rtitmuss/tornblue/img/PXL_20220306_111358722.jpg

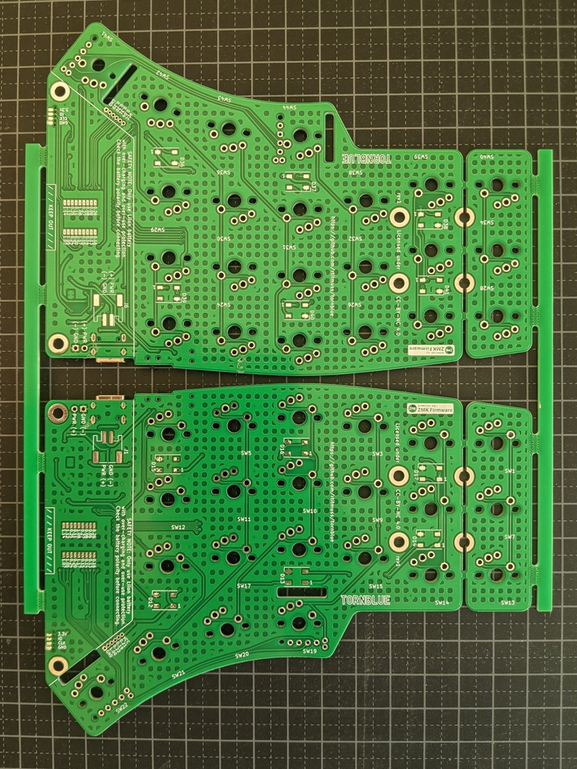
img/PXL_20220306_111358722.jpg
