rtitmuss/tornblue/pcb/tornblue.kicad_sch

## KiCad design pcb/tornblue.kicad_sch (2022-01-09)

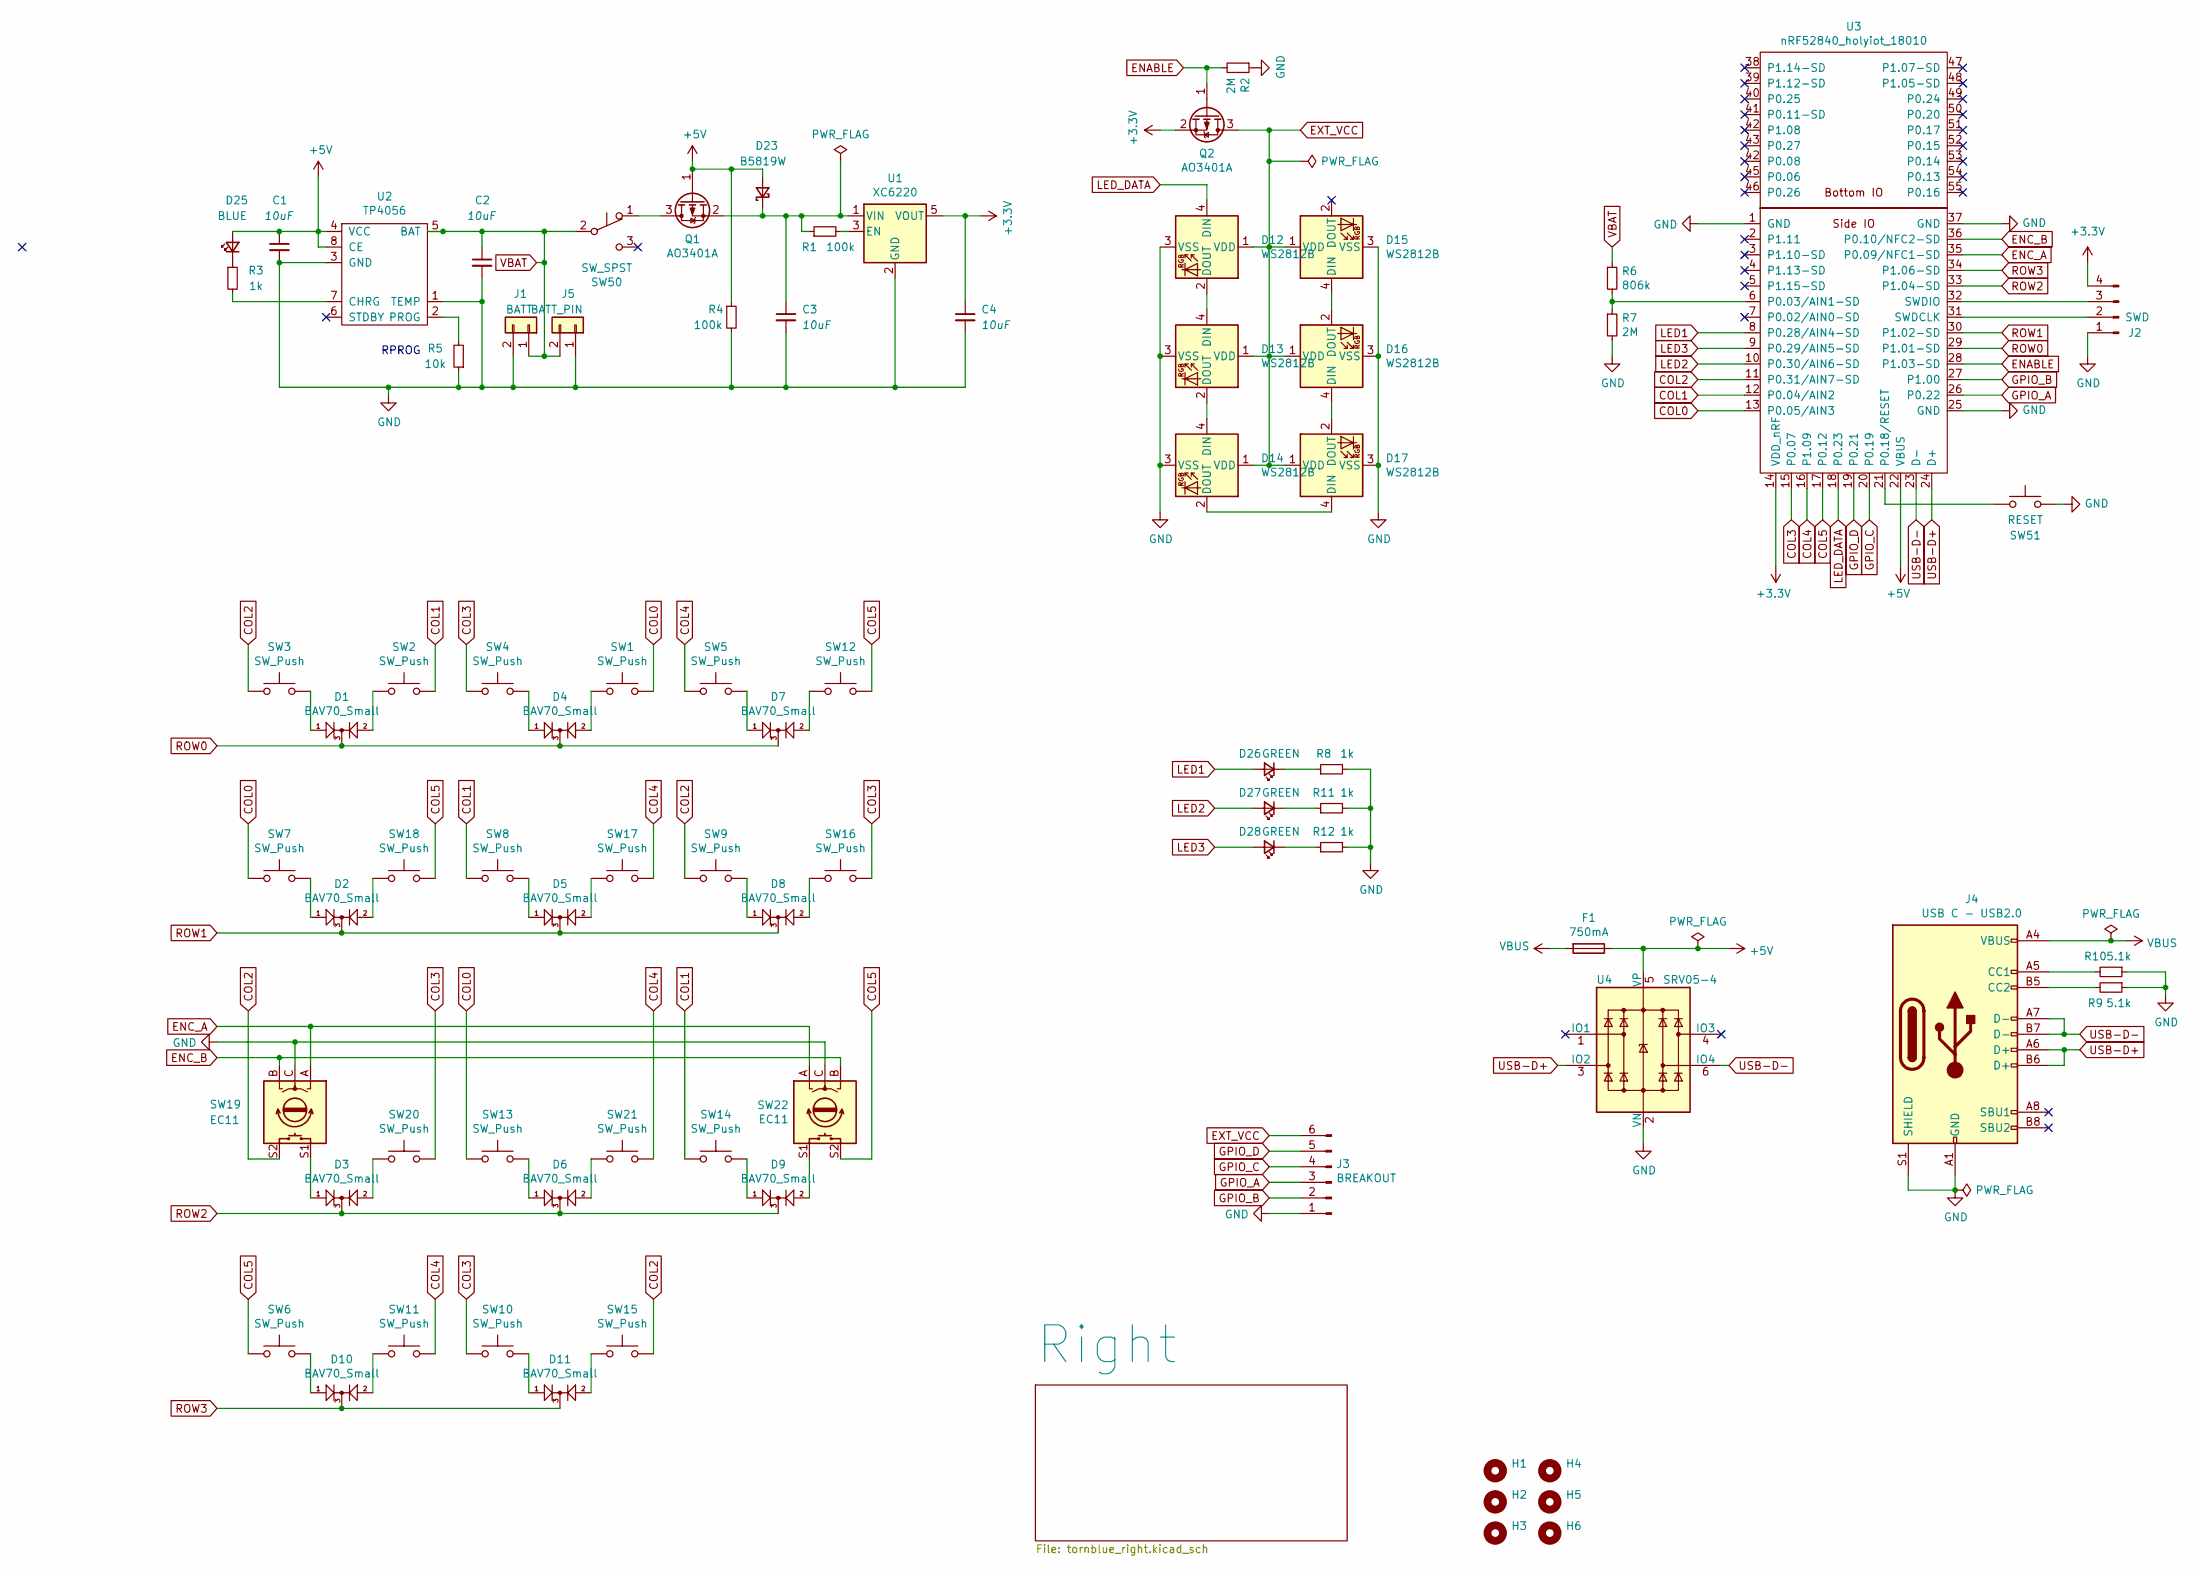
[picture p37: schematic tornblue.kicad_sch]

Parts:
C1, C2, C3, C4: 10uF; D_0805_2012Metric; PartNumber CL21A106KAYNNNE; LCSC C15850
D1, D2, D3, D4, D5, D6, D7, D8, D9, D10, D11: BAV70_Small; SOT-23; PartNumber BAV70; LCSC C68978
D12, D13, D14, D15, D16, D17: WS2812B; LED_WS2812B_PLCC4_5.0x5.0mm_P3.2mm; LCSC C2761795
D23: B5819W; D_SOD-123; PartNumber B5819W SL; LCSC C8598
D25: BLUE; LED_0805_2012Metric; PartNumber 17-21/BHC-AP1Q2/3T; LCSC C99870
D26, D27, D28: GREEN; LED_0805_2012Metric; PartNumber MHT170UGCT; LCSC C397047
F1: 750mA; Fuse_1206_3216Metric; PartNumber CC12H750MA-TR; LCSC C328915
H1, H2, H3, H4: MountingHole; MountingHole_3.2mm_M3_DIN965_Pad
H5, H6: MountingHole; MountingHole_3.2mm_M3_DIN965_Pad_Slot
J1: BATT; JST_PH_S2B-PH-SM4-TB_1x02-1MP_P2.00mm_Horizontal; LCSC C295747
J2: SWD; SOIC_clipProgSmall
J3: BREAKOUT; PinHeader_1x06_P1.27mm_Vertical
J4: USB C - USB2.0; USB_C_Receptacle_XKB_U262-16XN-4BVC11; PartNumber 918-418K2023S40001; LCSC C167321
J5: BATT_PIN; PinHeader_1x02_P2.54mm_Vertical
Q1, Q2: AO3401A; SOT-23; PartNumber AO3401A; LCSC C15127
R1, R4: 100k; R_0805_2012Metric; PartNumber 0805W8F1003T5E; LCSC C17407
R2, R7: 2M; R_0805_2012Metric; PartNumber 0805W8F2004T5E; LCSC C26112
R3, R8, R11, R12: 1k; R_0805_2012Metric; PartNumber 0805W8F1001T5E; LCSC C17513
R5: 10k; R_0805_2012Metric; PartNumber 0805W8F1002T5E; LCSC C17414
R6: 806k; R_0805_2012Metric; PartNumber 0805W8F8063T5E; LCSC C63494
R9, R10: 5.1k; R_0805_2012Metric; PartNumber 0805W8F5101T5E; LCSC C27834
SW1, SW2, SW3, SW4, SW5, SW6, SW7, SW8, SW9, SW10, SW11, SW12, SW13, SW14, SW15, SW16, SW17, SW18, SW20, SW21: SW_Push; MX_PG1350_optional
SW19, SW22: EC11; MX_PG1350_EVQWGD001_LR_optional
SW50: SW_SPST; SW_SPDT_PCM12; PartNumber PCM12SMTR; LCSC C221841
SW51: RESET; SW_SPST_EVQPUC02K; PartNumber EVQPUC02K; LCSC C79174
U1: XC6220; SOT-23-5; PartNumber XC6220B331MR-G; LCSC C86534
U2: TP4056; SOIC-8-1EP_3.9x4.9mm_P1.27mm_EP2.29x3mm_ThermalVias; PartNumber TP4056-42-ESOP8; LCSC C16581
U3: nRF52840_holyiot_18010; PartNumber YJ-18010-nRF52840; LCSC nRF52840_holyiot_18010
U4: SRV05-4; SOT-23-6; PartNumber SRV05-4-P-T7; LCSC C85364

Connections:
+3.3V: C4.1, J2.4, Q2.2 (S), U1.5 (VOUT), U3.14 (VDD_nRF)
+5V: C1.1, D23.2 (A), D25.2 (A), F1.1, Q1.1 (G), R4.1, U2.4 (VCC), U2.8 (CE), U3.22 (VBUS), U4.5 (VP)
COL0: SW1.1, SW7.1, SW13.1, U3.13 (P0.05/AIN3)
COL1: SW2.1, SW8.1, SW14.1, U3.12 (P0.04/AIN2)
COL2: SW3.1, SW9.1, SW15.1, SW19.S2, U3.11 (P0.31/AIN7-SD)
COL3: SW4.1, SW10.1, SW16.1, SW20.1, U3.15 (P0.07)
COL4: SW5.1, SW11.1, SW17.1, SW21.1, U3.16 (P1.09)
COL5: SW6.1, SW12.1, SW18.1, SW22.S2, U3.17 (P0.12)
ENABLE: Q2.1 (G), R2.2, U3.28 (P1.03-SD)
ENC_A: SW19.A, SW22.A, U3.35 (P0.09/NFC1-SD)
ENC_B: SW19.B, SW22.B, U3.36 (P0.10/NFC2-SD)
EXT_VCC: D12.1 (VDD), D13.1 (VDD), D14.1 (VDD), D15.1 (VDD), D16.1 (VDD), D17.1 (VDD), J3.6, Q2.3 (D)
GND: C1.2, C2.2, C3.2, C4.2, D12.3 (VSS), D13.3 (VSS), D14.3 (VSS), D15.3 (VSS), D16.3 (VSS), D17.3 (VSS), J1.2, J2.1, J3.1, J4.A1 (GND), J4.A12 (GND), J4.B1 (GND), J4.B12 (GND), J4.S1 (SHIELD), J5.1, R2.1, R4.2, R5.1, R7.2, R8.2, R9.1, R10.1, R11.2, R12.2, SW19.C, SW22.C, SW51.2, U1.2 (GND), U2.1 (TEMP), U2.3 (GND), U3.1 (GND), U3.25 (GND), U3.37 (GND), U4.2 (VN)
GPIO_A: J3.3, U3.26 (P0.22)
GPIO_B: J3.2, U3.27 (P1.00)
GPIO_C: J3.4, U3.20 (P0.19)
GPIO_D: J3.5, U3.19 (P0.21)
LED1: D26.2 (A), U3.8 (P0.28/AIN4-SD)
LED2: D27.2 (A), U3.10 (P0.30/AIN6-SD)
LED3: D28.2 (A), U3.9 (P0.29/AIN5-SD)
LED_DATA: D12.4 (DIN), U3.18 (P0.23)
unnamed: C3.1, D23.1 (K), Q1.2 (S), R1.1, U1.1 (VIN)
unnamed: D1.1 (A1), SW3.2
unnamed: D1.2 (A2), SW2.2
unnamed: D2.1 (A1), SW7.2
unnamed: D2.2 (A2), SW18.2
unnamed: D3.1 (A1), SW19.S1
unnamed: D3.2 (A2), SW20.2
unnamed: D4.1 (A1), SW4.2
unnamed: D4.2 (A2), SW1.2
unnamed: D5.1 (A1), SW8.2
unnamed: D5.2 (A2), SW17.2
unnamed: D6.1 (A1), SW13.2
unnamed: D6.2 (A2), SW21.2
unnamed: D7.1 (A1), SW5.2
unnamed: D7.2 (A2), SW12.2
unnamed: D8.1 (A1), SW9.2
unnamed: D8.2 (A2), SW16.2
unnamed: D9.1 (A1), SW14.2
unnamed: D9.2 (A2), SW22.S1
unnamed: D10.1 (A1), SW6.2
unnamed: D10.2 (A2), SW11.2
unnamed: D11.1 (A1), SW10.2
unnamed: D11.2 (A2), SW15.2
unnamed: D12.2 (DOUT), D13.4 (DIN)
unnamed: D13.2 (DOUT), D14.4 (DIN)
unnamed: D14.2 (DOUT), D17.4 (DIN)
unnamed: D15.4 (DIN), D16.2 (DOUT)
unnamed: D16.4 (DIN), D17.2 (DOUT)
unnamed: D25.1 (K), R3.1
unnamed: D26.1 (K), R8.1
unnamed: D27.1 (K), R11.1
unnamed: D28.1 (K), R12.1
unnamed: J2.2, U3.31 (SWDCLK)
unnamed: J2.3, U3.32 (SWDIO)
unnamed: J4.A5 (CC1), R10.2
unnamed: J4.B5 (CC2), R9.2
unnamed: Q1.3 (D), SW50.1 (A)
unnamed: R1.2, U1.3 (EN)
unnamed: R3.2, U2.7 (CHRG)
unnamed: R5.2, U2.2 (PROG)
unnamed: R6.2, R7.1, U3.6 (P0.03/AIN1-SD)
unnamed: SW51.1, U3.21 (P0.18/RESET)
ROW0: D1.3 (K), D4.3 (K), D7.3 (K), U3.29 (P1.01-SD)
ROW1: D2.3 (K), D5.3 (K), D8.3 (K), U3.30 (P1.02-SD)
ROW2: D3.3 (K), D6.3 (K), D9.3 (K), U3.33 (P1.04-SD)
ROW3: D10.3 (K), D11.3 (K), U3.34 (P1.06-SD)
USB-D+: J4.A6 (D+), J4.B6 (D+), U3.24 (D+), U4.3 (IO2)
USB-D-: J4.A7 (D-), J4.B7 (D-), U3.23 (D-), U4.6 (IO4)
VBAT: C2.1, J1.1, J5.2, R6.1, SW50.2 (B), U2.5 (BAT)
VBUS: F1.2, J4.A4 (VBUS), J4.A9 (VBUS), J4.B4 (VBUS), J4.B9 (VBUS)

Notes on the sheet:
RPROG
