rtitmuss/tornblue/pcb/tornblue_right.kicad_sch

## KiCad design pcb/tornblue_right.kicad_sch (2022-01-09)

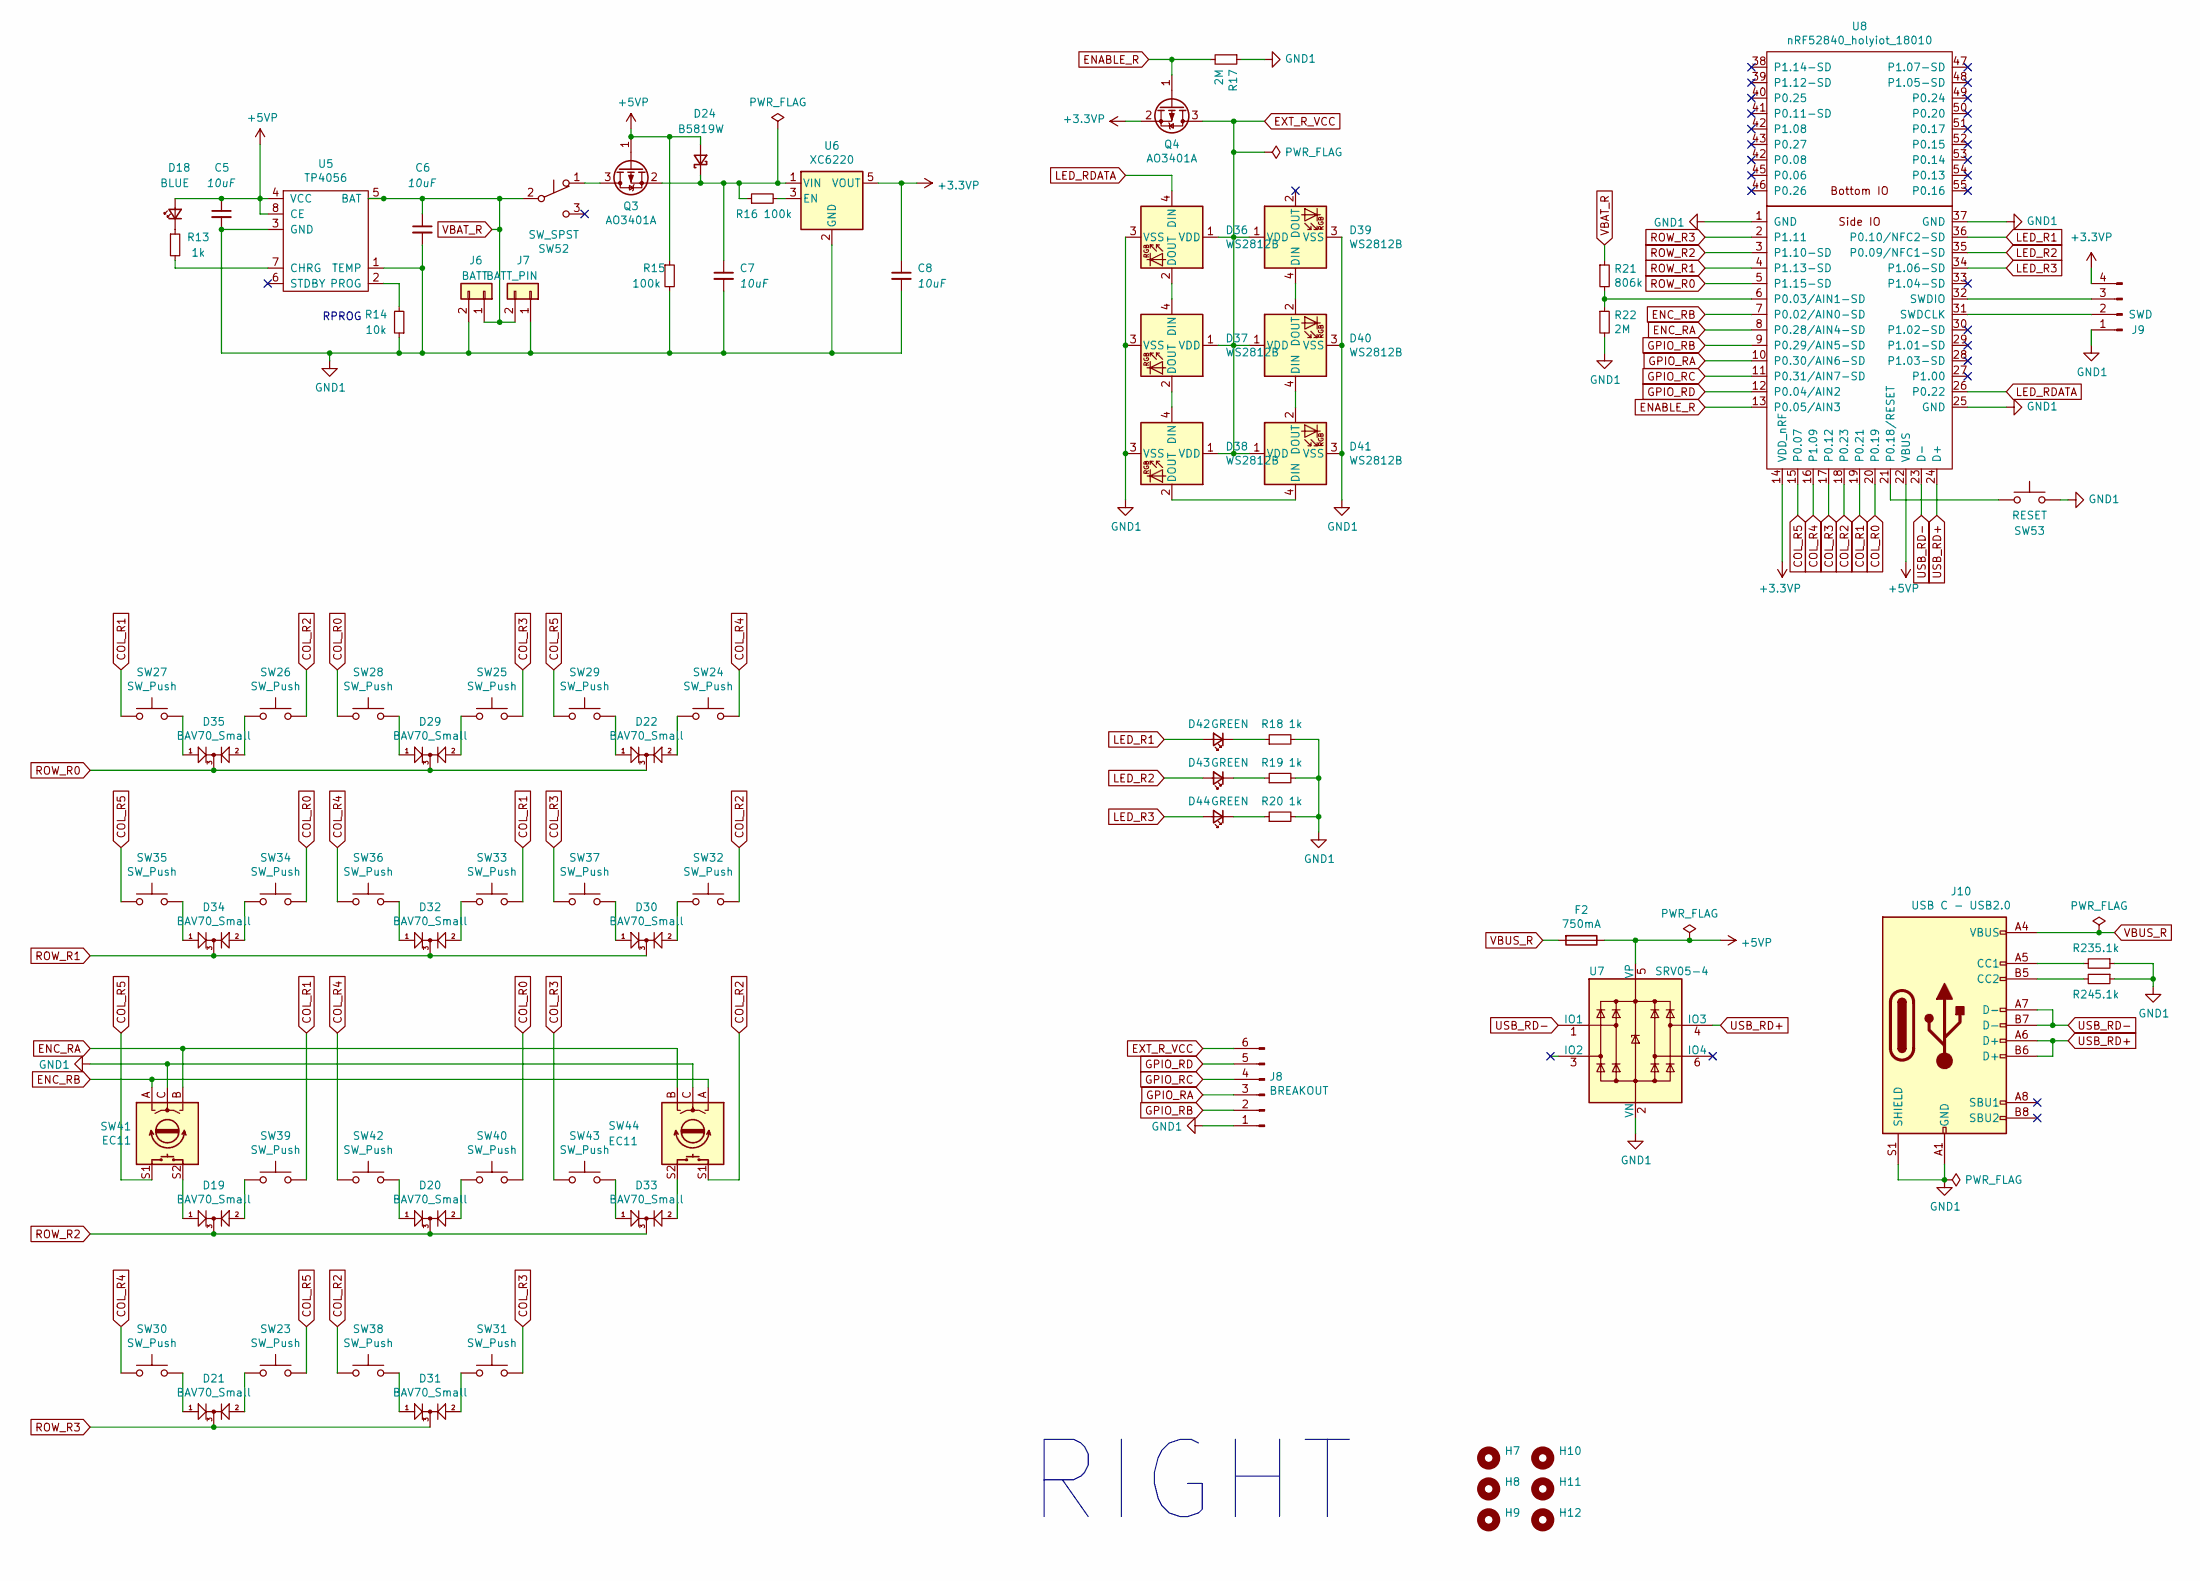
[picture p38: schematic tornblue_right.kicad_sch]

Parts:
C5, C6, C7, C8: 10uF; D_0805_2012Metric; PartNumber CL21A106KAYNNNE; LCSC C15850
D18: BLUE; LED_0805_2012Metric; PartNumber 17-21/BHC-AP1Q2/3T; LCSC C99870
D19, D20, D21, D22, D29, D30, D31, D32, D33, D34, D35: BAV70_Small; SOT-23; PartNumber BAV70; LCSC C68978
D24: B5819W; D_SOD-123; PartNumber B5819W SL; LCSC C8598
D36, D37, D38, D39, D40, D41: WS2812B; LED_WS2812B_PLCC4_5.0x5.0mm_P3.2mm; LCSC C2761795
D42, D43, D44: GREEN; LED_0805_2012Metric; PartNumber MHT170UGCT; LCSC C397047
F2: 750mA; Fuse_1206_3216Metric; PartNumber CC12H750MA-TR; LCSC C328915
H7, H8, H9, H10: MountingHole; MountingHole_3.2mm_M3_DIN965_Pad
H11, H12: MountingHole; MountingHole_3.2mm_M3_DIN965_Pad_Slot
J6: BATT; JST_PH_S2B-PH-SM4-TB_1x02-1MP_P2.00mm_Horizontal; LCSC C295747
J7: BATT_PIN; PinHeader_1x02_P2.54mm_Vertical
J8: BREAKOUT; PinHeader_1x06_P1.27mm_Vertical
J9: SWD; SOIC_clipProgSmall
J10: USB C - USB2.0; USB_C_Receptacle_XKB_U262-16XN-4BVC11; PartNumber 918-418K2023S40001; LCSC C167321
Q3, Q4: AO3401A; SOT-23; PartNumber AO3401A; LCSC C15127
R13, R18, R19, R20: 1k; R_0805_2012Metric; PartNumber 0805W8F1001T5E; LCSC C17513
R14: 10k; R_0805_2012Metric; PartNumber 0805W8F1002T5E; LCSC C17414
R15, R16: 100k; R_0805_2012Metric; PartNumber 0805W8F1003T5E; LCSC C17407
R17, R22: 2M; R_0805_2012Metric; PartNumber 0805W8F2004T5E; LCSC C26112
R21: 806k; R_0805_2012Metric; PartNumber 0805W8F8063T5E; LCSC C63494
R23, R24: 5.1k; R_0805_2012Metric; PartNumber 0805W8F5101T5E; LCSC C27834
SW23, SW24, SW25, SW26, SW27, SW28, SW29, SW30, SW31, SW32, SW33, SW34, SW35, SW36, SW37, SW38, SW39, SW40, SW42, SW43: SW_Push; MX_PG1350_optional
SW41, SW44: EC11; MX_PG1350_EVQWGD001_UD_optional
SW52: SW_SPST; SW_SPDT_PCM12; PartNumber PCM12SMTR; LCSC C221841
SW53: RESET; SW_SPST_EVQPUC02K; PartNumber EVQPUC02K; LCSC C79174
U5: TP4056; SOIC-8-1EP_3.9x4.9mm_P1.27mm_EP2.29x3mm_ThermalVias; PartNumber TP4056-42-ESOP8; LCSC C16581
U6: XC6220; SOT-23-5; PartNumber XC6220B331MR-G; LCSC C86534
U7: SRV05-4; SOT-23-6; PartNumber SRV05-4-P-T7; LCSC C85364
U8: nRF52840_holyiot_18010; PartNumber YJ-18010-nRF52840; LCSC nRF52840_holyiot_18010

Connections:
+3.3VP: C8.1, J9.4, Q4.2 (S), U6.5 (VOUT), U8.14 (VDD_nRF)
+5VP: C5.1, D18.2 (A), D24.2 (A), F2.1, Q3.1 (G), R15.1, U5.4 (VCC), U5.8 (CE), U7.5 (VP), U8.22 (VBUS)
COL_R0: SW28.1, SW34.1, SW40.1, U8.20 (P0.19)
COL_R1: SW27.1, SW33.1, SW39.1, U8.19 (P0.21)
COL_R2: SW26.1, SW32.1, SW38.1, SW44.S1, U8.18 (P0.23)
COL_R3: SW25.1, SW31.1, SW37.1, SW43.1, U8.17 (P0.12)
COL_R4: SW24.1, SW30.1, SW36.1, SW42.1, U8.16 (P1.09)
COL_R5: SW23.1, SW29.1, SW35.1, SW41.S1, U8.15 (P0.07)
ENABLE_R: Q4.1 (G), R17.2, U8.13 (P0.05/AIN3)
ENC_RA: SW41.B, SW44.B, U8.8 (P0.28/AIN4-SD)
ENC_RB: SW41.A, SW44.A, U8.7 (P0.02/AIN0-SD)
EXT_R_VCC: D36.1 (VDD), D37.1 (VDD), D38.1 (VDD), D39.1 (VDD), D40.1 (VDD), D41.1 (VDD), J8.6, Q4.3 (D)
GND1: C5.2, C6.2, C7.2, C8.2, D36.3 (VSS), D37.3 (VSS), D38.3 (VSS), D39.3 (VSS), D40.3 (VSS), D41.3 (VSS), J6.2, J7.1, J8.1, J9.1, J10.A1 (GND), J10.A12 (GND), J10.B1 (GND), J10.B12 (GND), J10.S1 (SHIELD), R14.1, R15.2, R17.1, R18.2, R19.2, R20.2, R22.2, R23.1, R24.1, SW41.C, SW44.C, SW53.2, U5.1 (TEMP), U5.3 (GND), U6.2 (GND), U7.2 (VN), U8.1 (GND), U8.25 (GND), U8.37 (GND)
GPIO_RA: J8.3, U8.10 (P0.30/AIN6-SD)
GPIO_RB: J8.2, U8.9 (P0.29/AIN5-SD)
GPIO_RC: J8.4, U8.11 (P0.31/AIN7-SD)
GPIO_RD: J8.5, U8.12 (P0.04/AIN2)
LED_R1: D42.2 (A), U8.36 (P0.10/NFC2-SD)
LED_R2: D43.2 (A), U8.35 (P0.09/NFC1-SD)
LED_R3: D44.2 (A), U8.34 (P1.06-SD)
LED_RDATA: D36.4 (DIN), U8.26 (P0.22)
unnamed: C7.1, D24.1 (K), Q3.2 (S), R16.1, U6.1 (VIN)
unnamed: D18.1 (K), R13.1
unnamed: D19.1 (A1), SW41.S2
unnamed: D19.2 (A2), SW39.2
unnamed: D20.1 (A1), SW42.2
unnamed: D20.2 (A2), SW40.2
unnamed: D21.1 (A1), SW30.2
unnamed: D21.2 (A2), SW23.2
unnamed: D22.1 (A1), SW29.2
unnamed: D22.2 (A2), SW24.2
unnamed: D29.1 (A1), SW28.2
unnamed: D29.2 (A2), SW25.2
unnamed: D30.1 (A1), SW37.2
unnamed: D30.2 (A2), SW32.2
unnamed: D31.1 (A1), SW38.2
unnamed: D31.2 (A2), SW31.2
unnamed: D32.1 (A1), SW36.2
unnamed: D32.2 (A2), SW33.2
unnamed: D33.1 (A1), SW43.2
unnamed: D33.2 (A2), SW44.S2
unnamed: D34.1 (A1), SW35.2
unnamed: D34.2 (A2), SW34.2
unnamed: D35.1 (A1), SW27.2
unnamed: D35.2 (A2), SW26.2
unnamed: D36.2 (DOUT), D37.4 (DIN)
unnamed: D37.2 (DOUT), D38.4 (DIN)
unnamed: D38.2 (DOUT), D41.4 (DIN)
unnamed: D39.4 (DIN), D40.2 (DOUT)
unnamed: D40.4 (DIN), D41.2 (DOUT)
unnamed: D42.1 (K), R18.1
unnamed: D43.1 (K), R19.1
unnamed: D44.1 (K), R20.1
unnamed: J9.2, U8.31 (SWDCLK)
unnamed: J9.3, U8.32 (SWDIO)
unnamed: J10.A5 (CC1), R23.2
unnamed: J10.B5 (CC2), R24.2
unnamed: Q3.3 (D), SW52.1 (A)
unnamed: R13.2, U5.7 (CHRG)
unnamed: R14.2, U5.2 (PROG)
unnamed: R16.2, U6.3 (EN)
unnamed: R21.2, R22.1, U8.6 (P0.03/AIN1-SD)
unnamed: SW53.1, U8.21 (P0.18/RESET)
ROW_R0: D22.3 (K), D29.3 (K), D35.3 (K), U8.5 (P1.15-SD)
ROW_R1: D30.3 (K), D32.3 (K), D34.3 (K), U8.4 (P1.13-SD)
ROW_R2: D19.3 (K), D20.3 (K), D33.3 (K), U8.3 (P1.10-SD)
ROW_R3: D21.3 (K), D31.3 (K), U8.2 (P1.11)
USB_RD+: J10.A6 (D+), J10.B6 (D+), U7.4 (IO3), U8.24 (D+)
USB_RD-: J10.A7 (D-), J10.B7 (D-), U7.1 (IO1), U8.23 (D-)
VBAT_R: C6.1, J6.1, J7.2, R21.1, SW52.2 (B), U5.5 (BAT)
VBUS_R: F2.2, J10.A4 (VBUS), J10.A9 (VBUS), J10.B4 (VBUS), J10.B9 (VBUS)

Notes on the sheet:
RIGHT
RPROG
